pablogs9/RocketFPGA/Software/FPGA Sample Code/Mixer/main.v

module main(
    //49.152MHz MHz clock
    input OSC,

    //SPI Interface
    output wire SCLK,
    output wire MOSI,
    output wire CS,

    output wire IO7,
    output wire IO6,
    output wire IO5,
    output wire IO4,


    //I2S Interface
    output wire MCLK,
    input wire BCLK,
    input wire ADCLRC,
    input wire DACLRC,
    input wire ADCDAT,
    output wire DACDAT,

    output wire LED,
    input wire RESET,
    input wire USER_BUTTON,

    output wire PRE_RESET,
    input wire RXD,

    output wire CAPACITOR,
    output wire POT_1,
    output wire POT_2,
    input wire DIFF_IN,
);

localparam BITSIZE = 24;

// Clocking and reset
reg [30:0] divider;
always @(posedge OSC) begin
    divider <= divider + 1;
end

assign MCLK = divider[1]; //12.288 MHz

configurator #(
    .BITSIZE(BITSIZE),
    .LINE_NOMIC(1'b0),
)conf (
    .clk(divider[6]),
    .spi_mosi(MOSI), 
    .spi_sck(SCLK),
    .cs(CS),
    .prereset(PRE_RESET),
);

// Path
wire [BITSIZE-1:0] sine1;
wire [BITSIZE-1:0] sine2;
wire [BITSIZE-1:0] sine3;
wire [BITSIZE-1:0] sine4;

wire [BITSIZE-1:0] mic;
wire [BITSIZE-1:0] m1_out;
wire [BITSIZE-1:0] out;

i2s_rx #( 
  .BITSIZE(BITSIZE),
) I2SRX (
  .sclk (BCLK), 
  .lrclk (ADCLRC),
  .sdata (ADCDAT),
  .left_chan (mic),
);

sinegenerator #(
    .BITSIZE(BITSIZE),
    .PHASESIZE(16),
) S1 (
    .enable(1'b1),
	.lrclk(DACLRC),
    .out(sine1),
    .freq(300), // 220 Hz
);

sinegenerator #(
    .BITSIZE(BITSIZE),
    .PHASESIZE(16),
) S2 (
    .enable(1'b1),
	.lrclk(DACLRC),
    .out(sine2),
    .freq(1201), // 880 Hz
);

// sinegenerator #(
//     .BITSIZE(BITSIZE),
//     .PHASESIZE(16),
// ) S3 (
//     .enable(1'b1),
// 	.lrclk(DACLRC),
//     .out(sine3),
//     .freq(2403), // 1760 Hz
// );

// sinegenerator #(
//     .BITSIZE(BITSIZE),
//     .PHASESIZE(16),
// ) S4 (
//     .enable(1'b1),
// 	.lrclk(DACLRC),
//     .out(sine4),
//     .freq(9612), // 7040 Hz
// );

// mixer4_fixed #(
//     .BITSIZE(BITSIZE),
// ) M1 (
// 	.lrclk(DACLRC),
// 	.bclk(BCLK),
// 	.in1(sine1),
// 	.in2(sine2),
//     .in3(sine3),
// 	.in4(sine4),
//     .out(m1_out),
// );

mixer2_fixed #(
    .BITSIZE(BITSIZE),
) M2 (
	.lrclk(DACLRC),
	.bclk(BCLK),
	.in1(sine1),
	.in2(sine2),
    .out(out),
);

i2s_tx #( 
    .BITSIZE(BITSIZE),
) I2STX (
    .sclk (BCLK), 
    .lrclk (DACLRC),
    .sdata (DACDAT),
    .left_chan (out),
    .right_chan (out)
);

endmodule
