pablogs9/RocketFPGA/Software/FPGA Sample Code/Echo/memory.v

module memory #(
	parameter BITSIZE = 24,
  parameter LENGHT = 1,
)(	

    input wire clk,

    input wire [ADDRLEN-1:0] addr,
    input wire [BITSIZE-1:0] datain,
    output reg [BITSIZE-1:0] dataout,
    	
    input wire wren,
);

localparam ADDRLEN = (LENGHT == 4) ? 16 : ((LENGHT == 2) ? 15 : 14);

if (LENGHT == 4) begin
  localparam MEMLEN = ADDRLEN - 2;
  wire [3:0] chipselect;

  assign chipselect[0] = (addr[ADDRLEN-1:ADDRLEN-2] == 2'b00);
  assign chipselect[1] = (addr[ADDRLEN-1:ADDRLEN-2] == 2'b01);
  assign chipselect[2] = (addr[ADDRLEN-1:ADDRLEN-2] == 2'b10);
  assign chipselect[3] = (addr[ADDRLEN-1:ADDRLEN-2] == 2'b11);

  wire [BITSIZE-1:0] outbuff [0:3];
  assign dataout = outbuff[addr[ADDRLEN-1:ADDRLEN-2]];
end else if (LENGHT == 2) begin
    localparam MEMLEN = ADDRLEN - 1;
    wire [1:0] chipselect;

    assign chipselect[0] = (addr[ADDRLEN-1] == 1'b0);
    assign chipselect[1] = (addr[ADDRLEN-1] == 1'b1);

    wire [BITSIZE-1:0] outbuff [0:1];
    assign dataout = outbuff[addr[ADDRLEN-1]];
end else if (LENGHT == 1) begin
    localparam MEMLEN = ADDRLEN;
    wire [1:0] chipselect;

    assign chipselect[0] = 1'b1;

    wire [BITSIZE-1:0] outbuff [1:0];
    assign dataout = outbuff[0];
end


SB_SPRAM256KA M1 (
  .ADDRESS (addr[MEMLEN-1:0]), 
  .DATAIN (datain), 
  .DATAOUT (outbuff[0]),
  .MASKWREN (4'b1111),
  .WREN (wren),
  .CHIPSELECT (chipselect[0]),
  .CLOCK (clk),
  .STANDBY (1'b0),
  .SLEEP (1'b0),
  .POWEROFF (1'b1)
);

if (LENGHT >= 2) begin
  SB_SPRAM256KA M2 (
    .ADDRESS (addr[MEMLEN-1:0]), 
    .DATAIN (datain), 
    .DATAOUT (outbuff[1]),
    .MASKWREN (4'b1111),
    .WREN (wren),
    .CHIPSELECT (chipselect[1]),
    .CLOCK (clk),
    .STANDBY (1'b0),
    .SLEEP (1'b0),
    .POWEROFF (1'b1)
  );
end

if (ADDRLEN >= 4) begin
  SB_SPRAM256KA M3 (
    .ADDRESS (addr[MEMLEN-1:0]), 
    .DATAIN (datain), 
    .DATAOUT (outbuff[2]),
    .MASKWREN (4'b1111),
    .WREN (wren),
    .CHIPSELECT (chipselect[2]),
    .CLOCK (clk),
    .STANDBY (1'b0),
    .SLEEP (1'b0),
    .POWEROFF (1'b1)
  );

  SB_SPRAM256KA M4 (
    .ADDRESS (addr[MEMLEN-1:0]), 
    .DATAIN (datain), 
    .DATAOUT (outbuff[3]),
    .MASKWREN (4'b1111),
    .WREN (wren),
    .CHIPSELECT (chipselect[3]),
    .CLOCK (clk),
    .STANDBY (1'b0),
    .SLEEP (1'b0),
    .POWEROFF (1'b1)
  );
end

endmodule
